Midlandswim/SmartChart-DMAC/Miscellaneous/Old Slideshow/HOSA Medical Innovation Slides.pdf

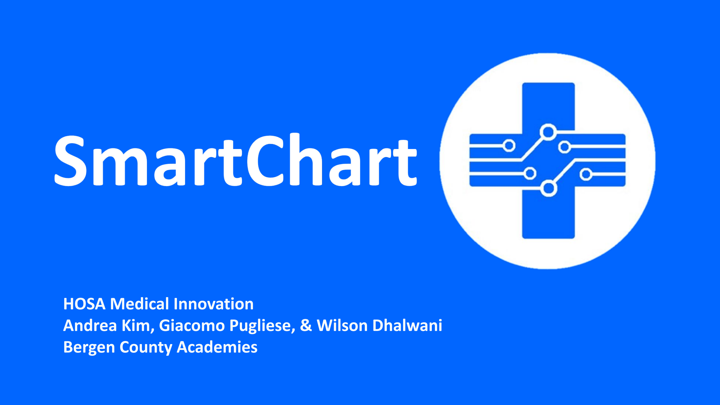
[picture p6: page 1]

HOSA Medical Innovation
Andrea Kim, Giacomo Pugliese, & Wilson Dhalwani Bergen County Academies

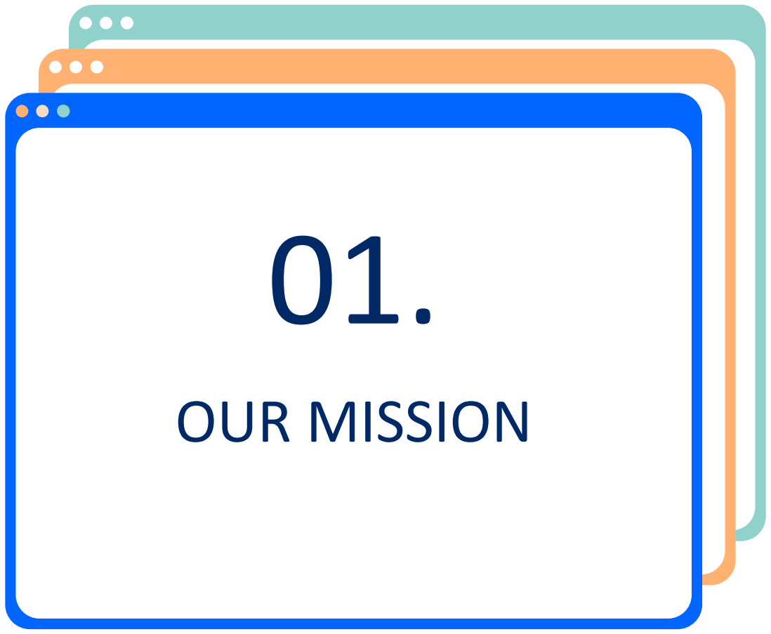
[picture p7: figure]
OUR MISSION

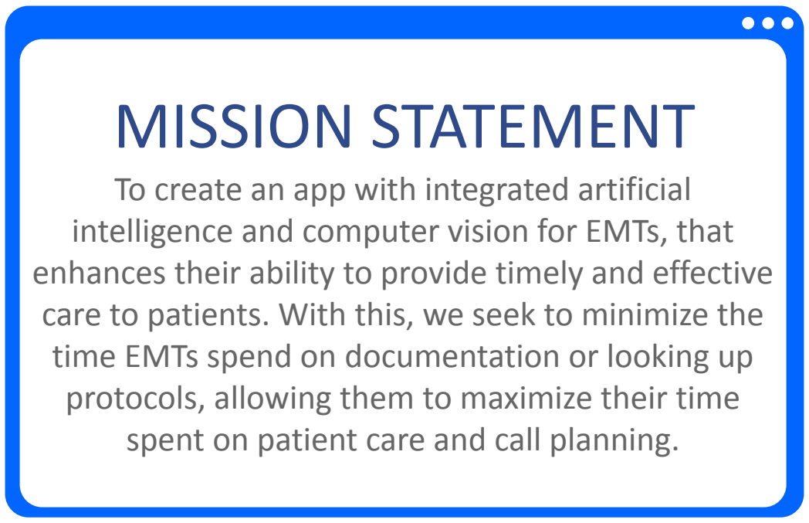
[picture p8: figure]
MISSION STATEMENT

To create an app with integrated artificial intelligence and computer vision for EMTs, that enhances their ability to provide timely and effective care to patients. With this, we seek to minimize the time EMTs spend on documentation or looking up protocols, allowing them to maximize their time spent on patient care and call planning.

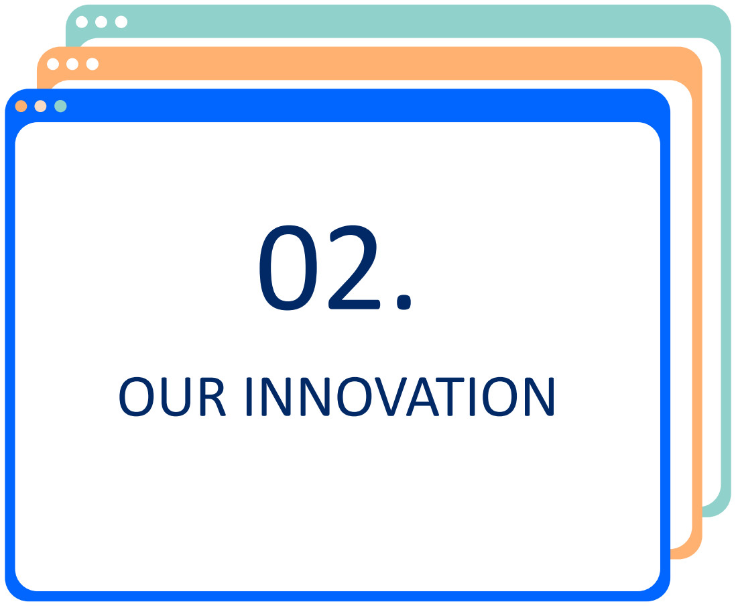
[picture p9: figure]
OUR INNOVATION

Created an artificial intelligence integrated web application, SmartChart, designed for the efficient and consistent delivery of EMS care.

- 5 pages
- Patient Chart
■ An interface for EMTs to record vitals
- Recommended Actions
■ Live updating patient care suggestions tab
- Patient Communication
■ On-demand translations for language barriers
- Patient Assessment
■ Machine learning model to take in and classify images
- Transport Directions
■ Provides directions to recommended medical facilities.

## PRACTITIONERS & TRAINING REQUIREMENTS

- This app is created for EMTs to use on-duty. Users of this web app must be a certified EMT in order to ensure that they the background knowledge and training necessary to correctly carry-out actions.

## COST ANALYSIS

- This web app will be made free to all users in order provide quality healthcare to all people.

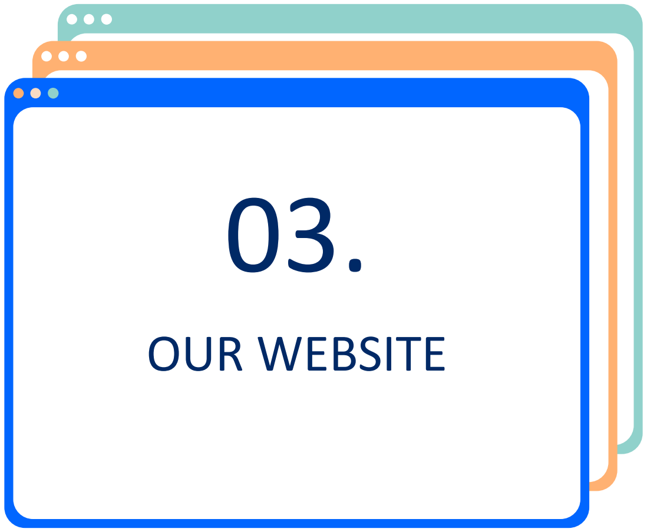
[picture p10: figure]
OUR WEBSITE

## WEBSITE CONTENTS

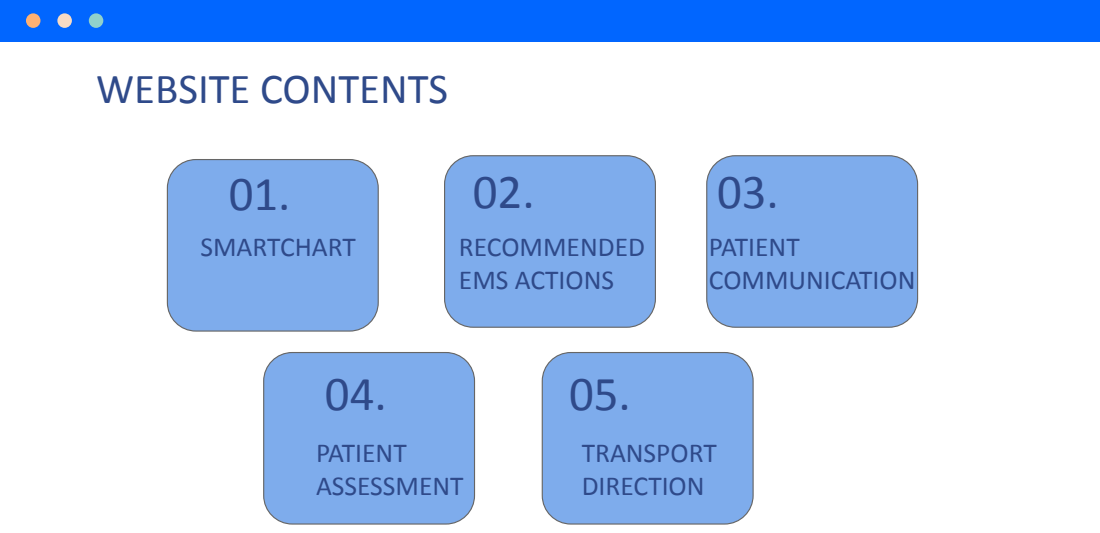
[picture p11: page 8]
SMARTCHART; TRANSPORT DIRECTION; RECOMMENDED EMS ACTIONS; PATIENT ASSESSMENT; PATIENT COMMUNICATION

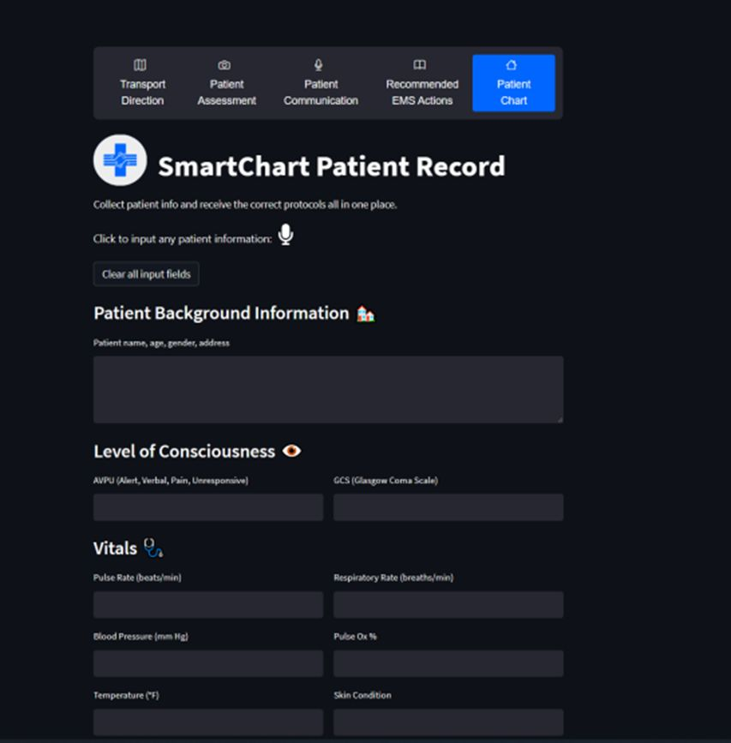
[picture p12: figure]

- Manual and voice input options
- Voice input saves time
- Effective speech recognition using AI to understand speech patterns

## PATIENT CHART

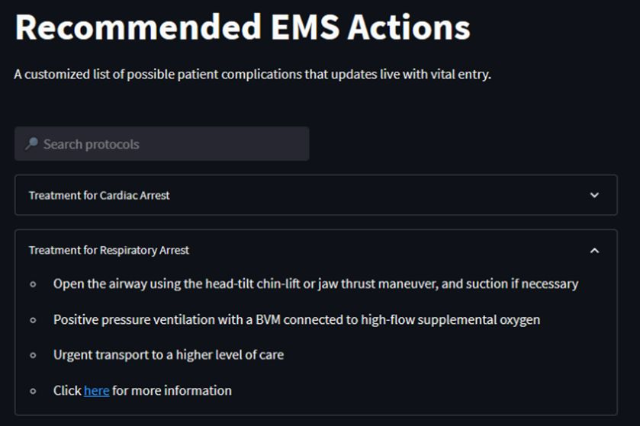
[picture p13: figure]

- Search feature to find specific complications
- List of recommended actions
- Adjusts to the patient’s vitals

## RECOMMENDED EMS ACTIONS

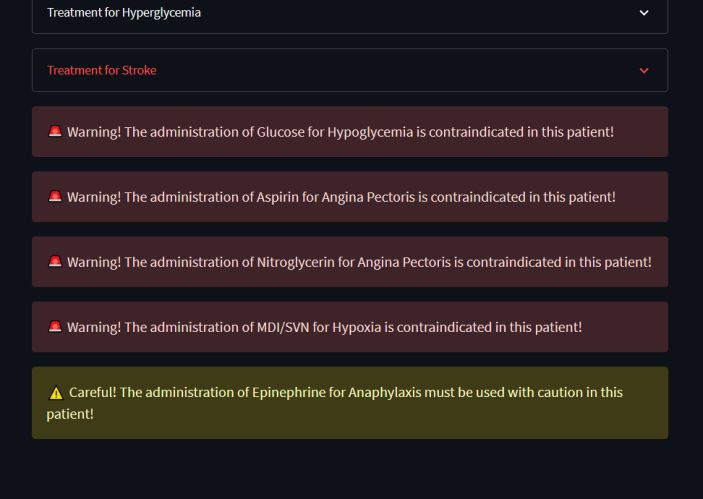
[picture p14: figure]

### - Each result also indicates possible contraindications and relative contraindications based on the patient’s vitals

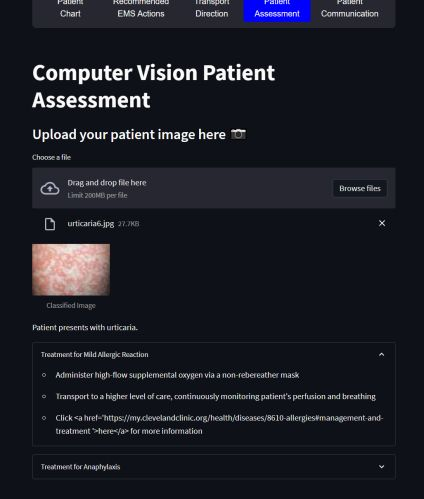
[picture p15: figure]

- Uses machine learning to classify patient signs and symptoms
- Also gives relevant protocol materials for the EMT

## PATIENT ASSESSMENT

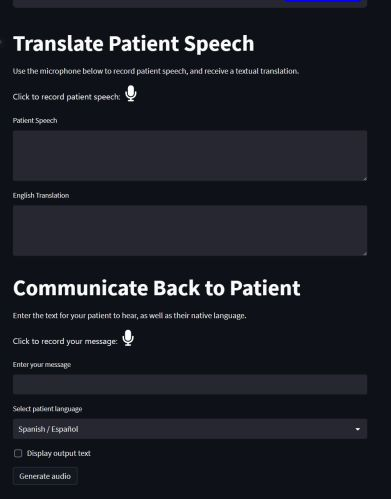
[picture p16: figure]

- On-demand translations help with language barriers
- Conversations can be recorded or typed
- 10 language options to translate the EMT or the patient’s message

## PATIENT COMMUNICATION

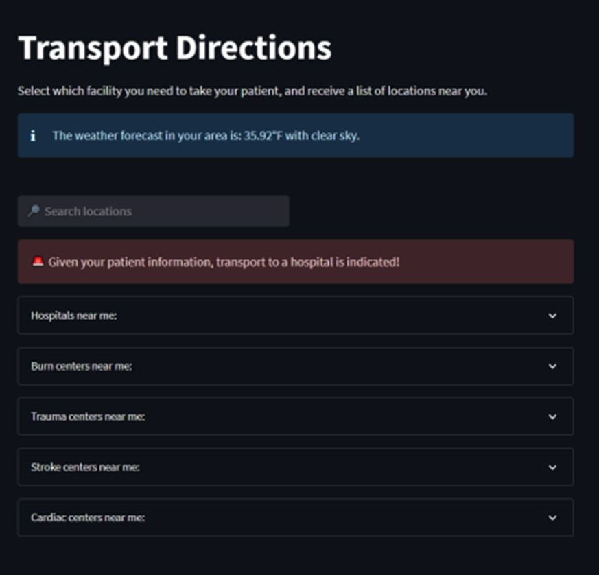
[picture p17: figure]

- Alerts EMT about weather conditions
- Provides a list of the nearest facilities

## TRANSPORT DIRECTIONS

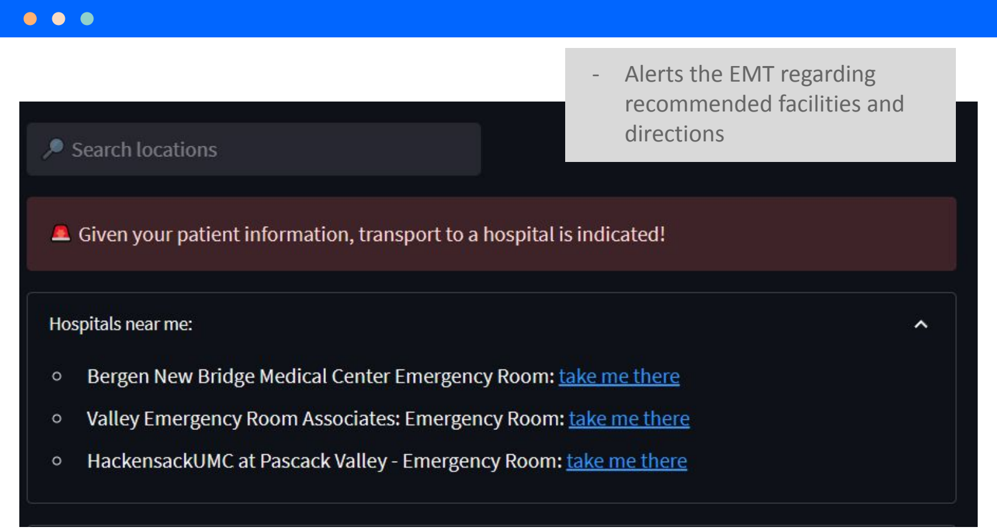
[picture p18: page 15]

- Alerts the EMT regarding recommended facilities and directions

## IMPACT ON FUTURE INNOVATION

Our goal is to empower EMTs with the tools and knowledge they need to save lives, reduce patient morbidity and mortality, and improve the overall quality of emergency medical care. We hope that by using our app, patients can receive faster and more accurate diagnoses as well as receive the quality treatment they need.

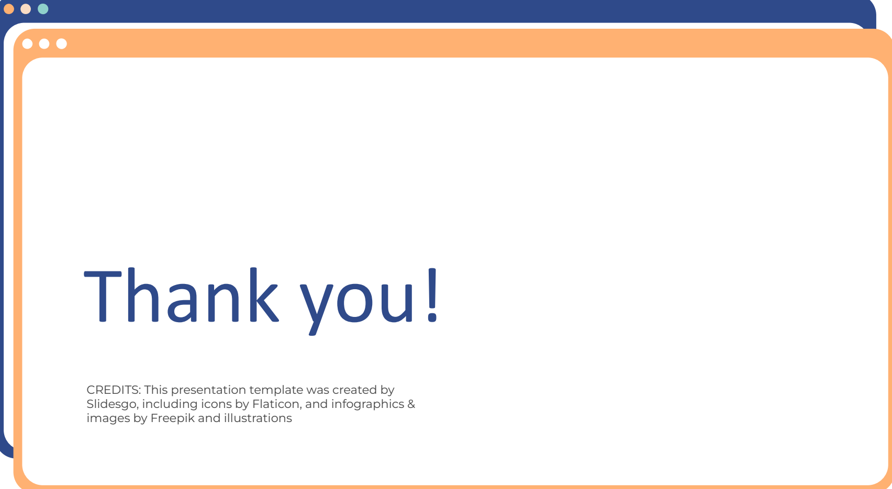
[picture p19: figure]
images by Freepik and illustrations; Thank you!

CREDITS: This presentation template was created by Slidesgo, (http://bit.ly/2Tynxth) including icons by Flaticon, (http://bit.ly/2TyoMsr) and infographics &
