Midlandswim/SmartChart-DMAC/Visuals/Photos/HOSACaseDecalPic.jpg

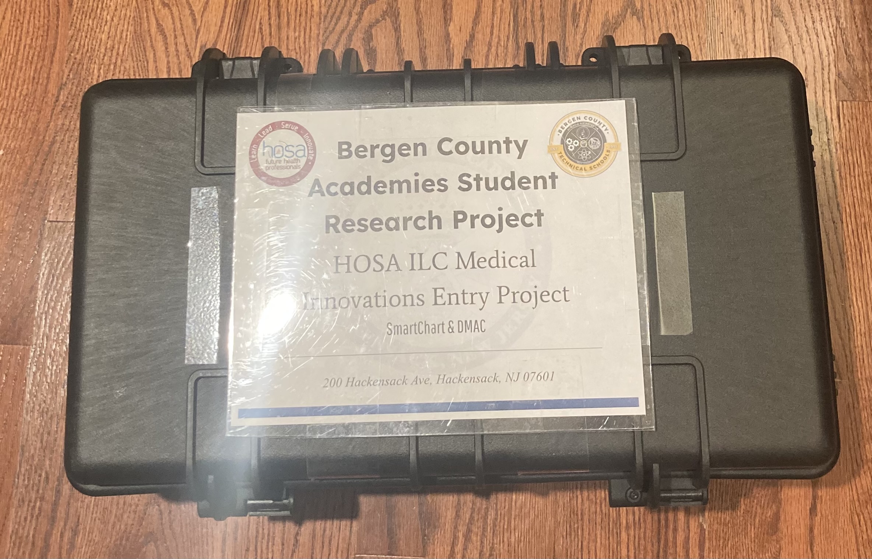
Visuals/Photos/HOSACaseDecalPic.jpg
