Midlandswim/SmartChart-DMAC/Visuals/Photos/HOSAExhibitPic.jpg

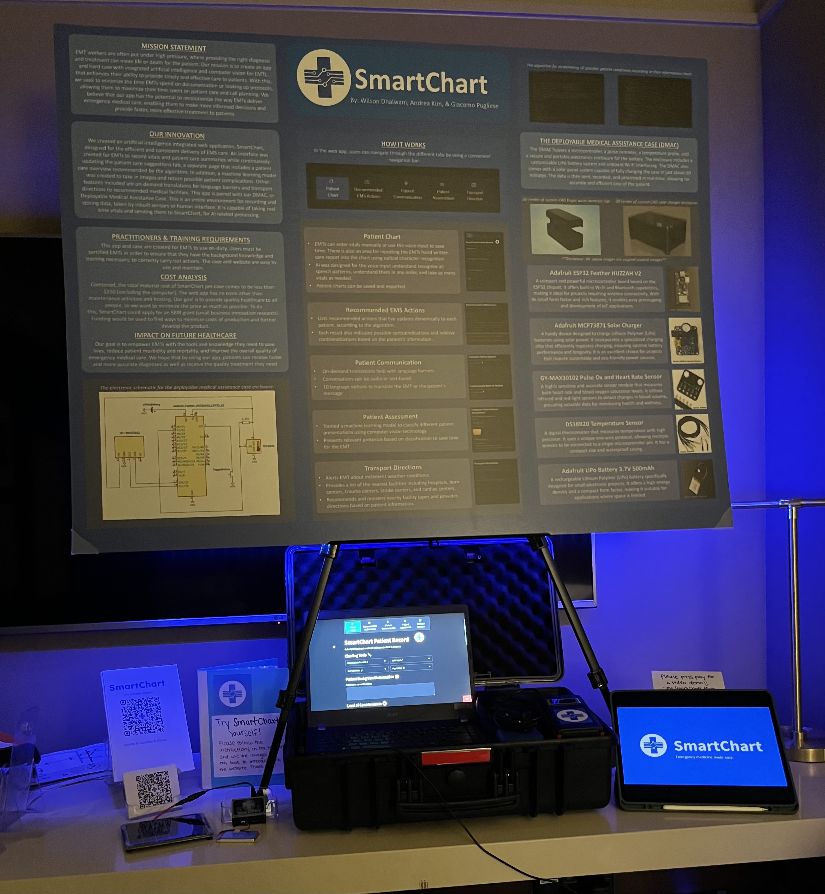
Visuals/Photos/HOSAExhibitPic.jpg
