Midlandswim/SmartChart-DMAC/Visuals/Photos/HOSAPlanePic.jpg

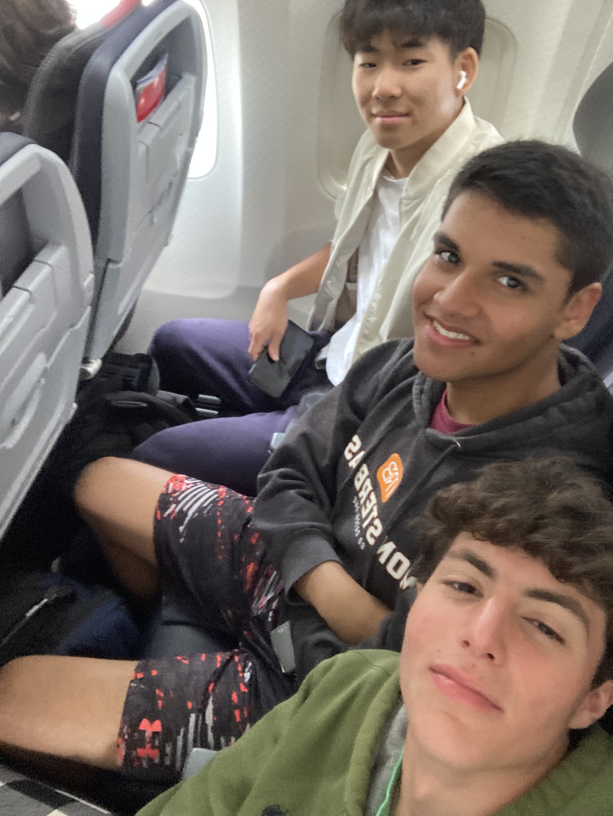
Visuals/Photos/HOSAPlanePic.jpg
