Midlandswim/SmartChart-DMAC/Visuals/Photos/IMG_8310.jpg

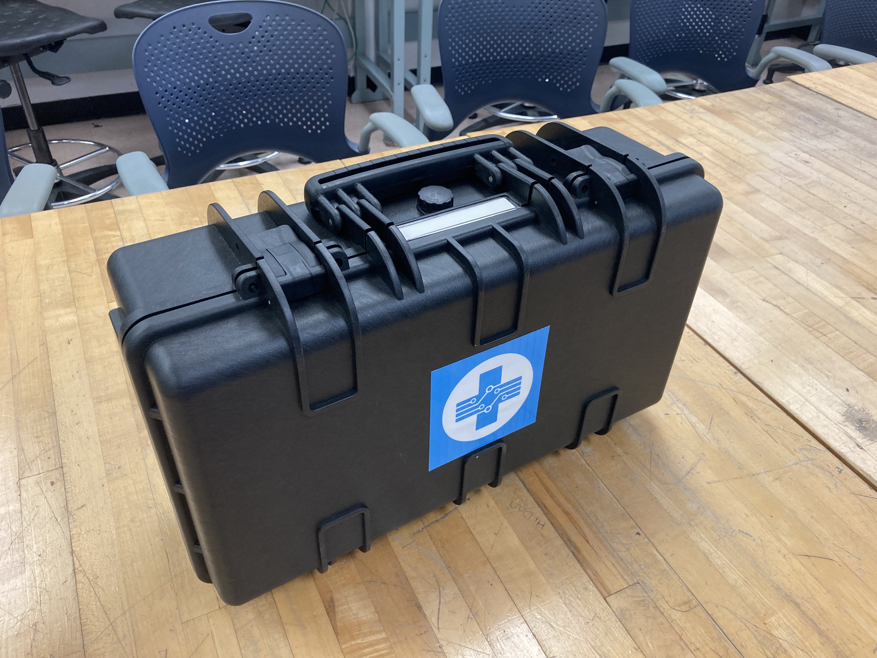
Visuals/Photos/IMG_8310.jpg
