Midlandswim/SmartChart-DMAC/Visuals/Renders/GY-MAX30102PCBRender3.png

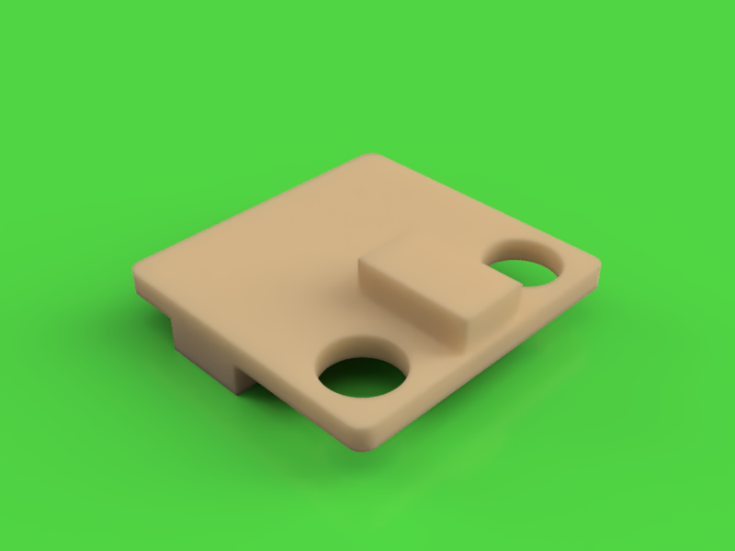
Visuals/Renders/GY-MAX30102PCBRender3.png
