Midlandswim/SmartChart-DMAC/Visuals/Renders/GY-MAX30102PCBRender.png

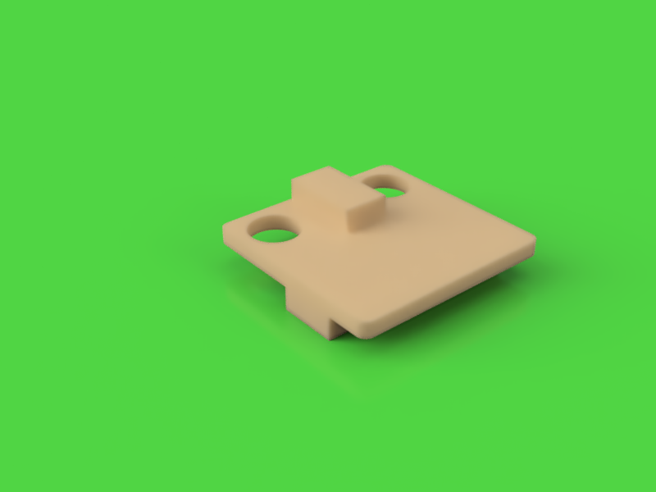
Visuals/Renders/GY-MAX30102PCBRender.png
