Midlandswim/SmartChart-DMAC/Visuals/Renders/image (8).png

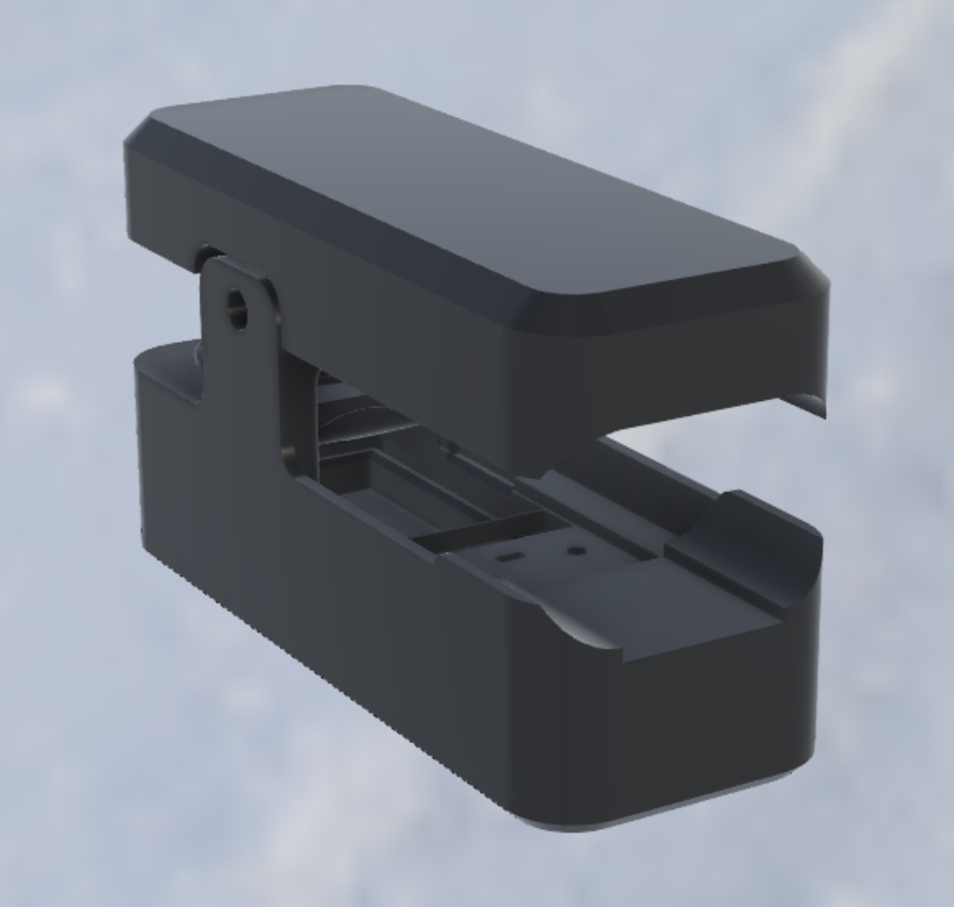
Visuals/Renders/image (8).png
