Midlandswim/SmartChart-DMAC/Visuals/Renders/MCP73871Render1.png

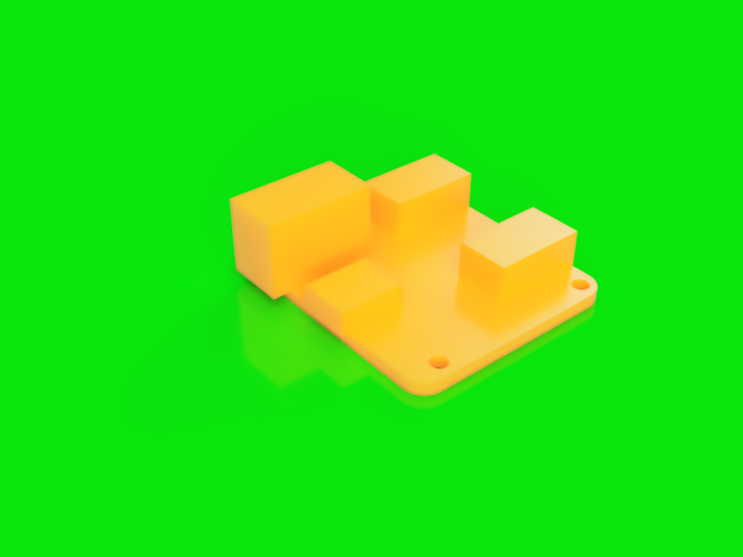
Visuals/Renders/MCP73871Render1.png
