Midlandswim/SmartChart-DMAC/Visuals/Renders/MCP73871Render2.png

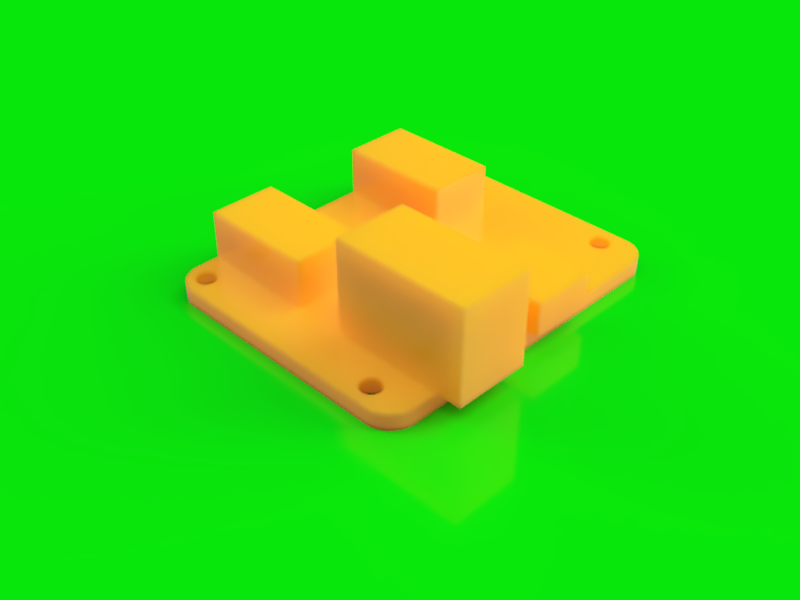
Visuals/Renders/MCP73871Render2.png
