Midlandswim/SmartChart-DMAC/Visuals/Renders/PulseOxiRender1.png

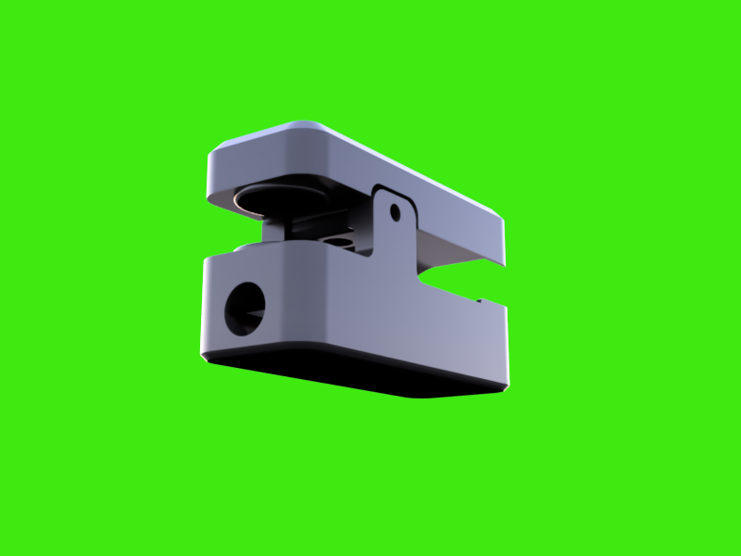
Visuals/Renders/PulseOxiRender1.png
