Midlandswim/SmartChart-DMAC/Visuals/Renders/PulseOxiRender2.png

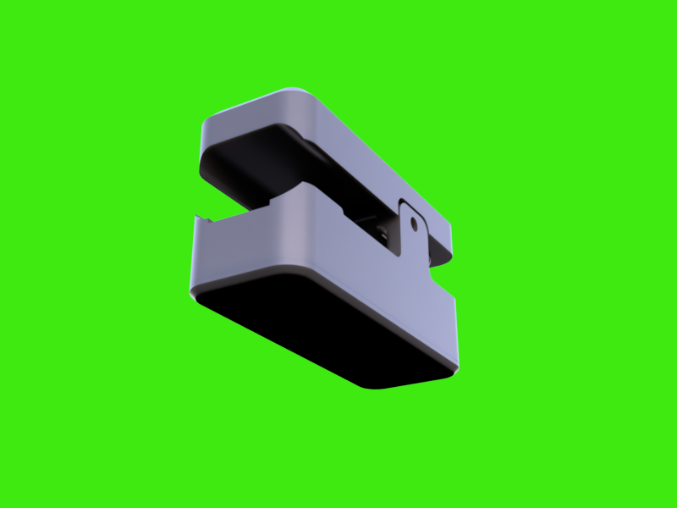
Visuals/Renders/PulseOxiRender2.png
