Midlandswim/SmartChart-DMAC/Visuals/Renders/PulseOxiRender3.png

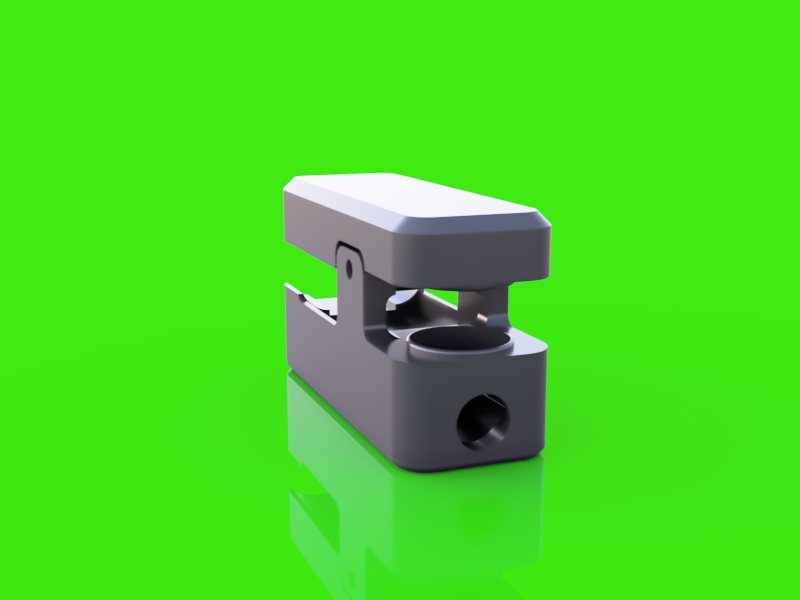
Visuals/Renders/PulseOxiRender3.png
