Midlandswim/SmartChart-DMAC/Visuals/Renders/PulseOxiRender4.png

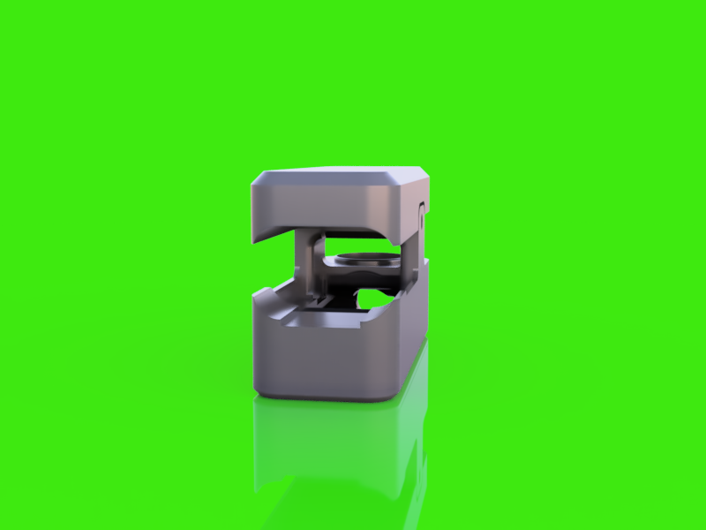
Visuals/Renders/PulseOxiRender4.png
