Midlandswim/SmartChart-DMAC/Visuals/Renders/PulseOxiRender5.png

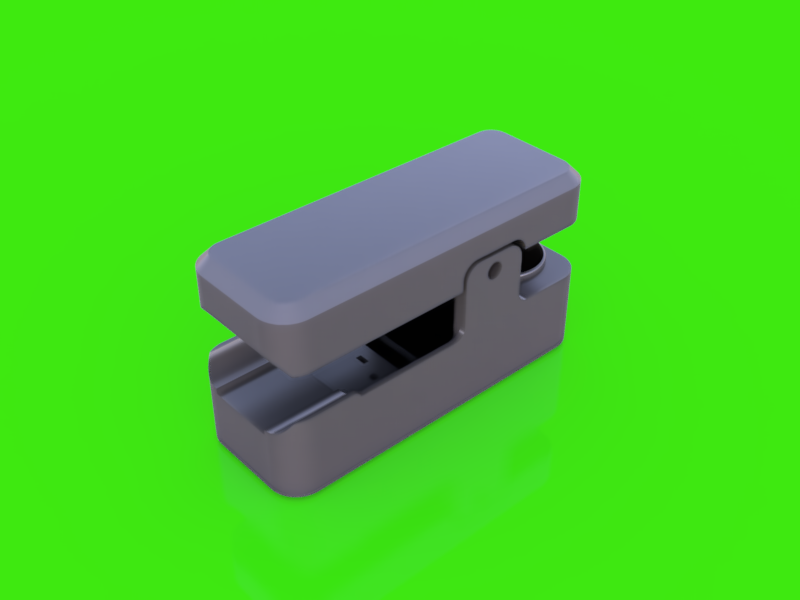
Visuals/Renders/PulseOxiRender5.png
